Neumi/wifi_camera/wifi_mapper/stack_data/images/csv_file_1637193311.csv.png

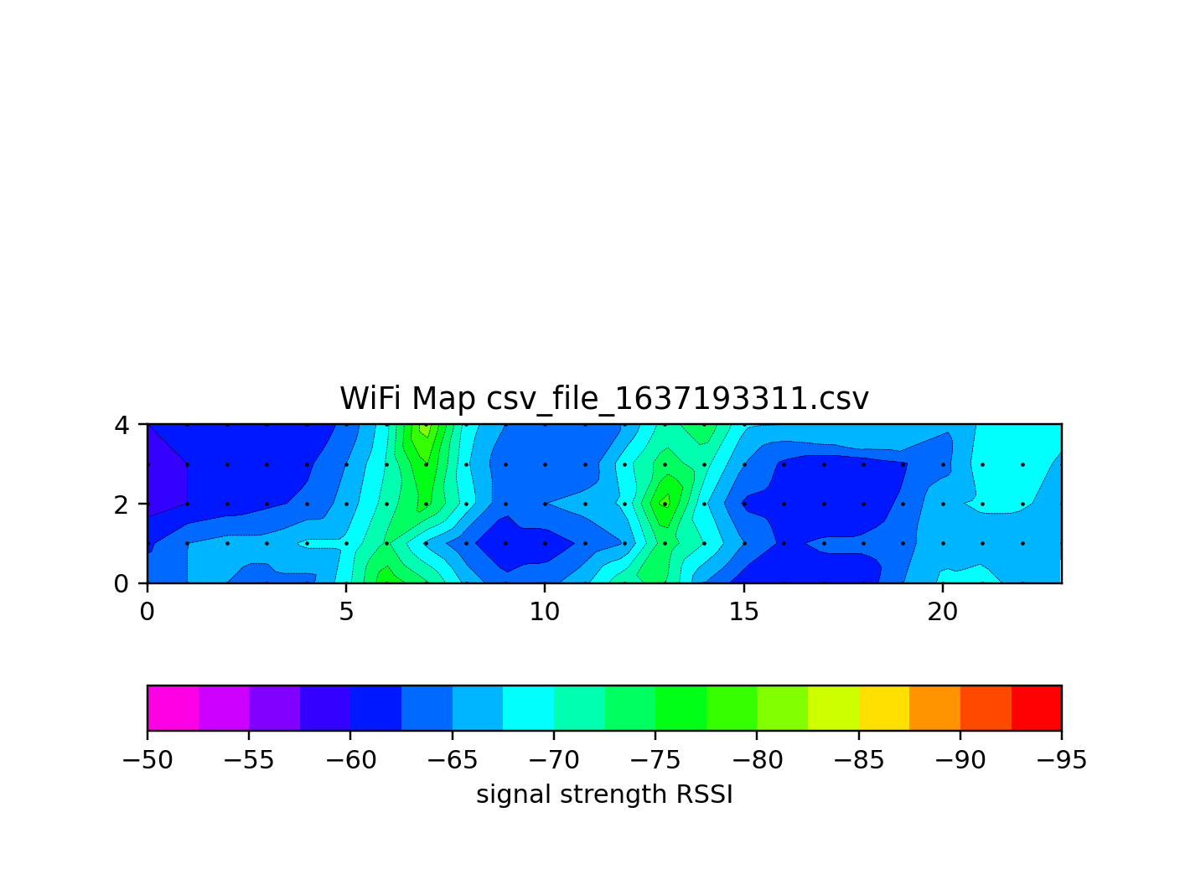
wifi_mapper/stack_data/images/csv_file_1637193311.csv.png
